ki6syd/minimalist-amateur-xcvr/hw/audio/max-3b_2-2.asc

C1: cap; 100n
C2: cap; 1n
C3: cap; 47n
C4: cap; 1n
C5: cap; 36n
C6: cap; 1n
C7: cap; 39n
C8: cap; 2.2n
C9: cap; 2.2n
C10: cap; 10µ
C11: cap; 10p
C12: cap; 1n
C13: cap; 2n
R1: res; 33k
R2: res; 33k
R3: res; 33k
R4: res; 47k
R5: res; 47k
R6: res; 36k
R7: res; 36k
R8: res; 10k
R9: res; 750k
R10: res; 22k
R11: res; 1k
R12: res; {Rdiv}
R13: res; 49.9k
R14: res; 49.9k
U1: UniversalOpAmp
U2: UniversalOpAmp
U3: UniversalOpAmp
U4: UniversalOpAmp
U5: UniversalOpAmp
V1: voltage; SINE(1.65 10m 700); AC 1
V2: voltage; 3.3
V3: voltage; 1.65
Named nets: 0, VDD, LPF1, LPF2, LPF3, HPF, OUT, IN, VMID, SSB-FILT
*.tran 0 110m 100m
.ac dec 100 100 10k
.step param Rdiv list 100 1Meg
Add 10k to reduce gain
