ki6syd/minimalist-amateur-xcvr/fw/Queue.h

/*
 * Queue.h
 * 
 * By Steven de Salas
 * 
 * Defines a templated (generic) class for a queue of things.
 * Used for Arduino projects, just #include "Queue.h" and add this file via the IDE.
 * 
 * Examples:
 * 
 * Queue<char> queue(10); // Max 10 chars in this queue
 * queue.push('H');
 * queue.push('e');
 * queue.count(); // 2
 * queue.push('l');
 * queue.push('l');
 * queue.count(); // 4
 * Serial.print(queue.pop()); // H
 * Serial.print(queue.pop()); // e
 * queue.count(); // 2
 * queue.push('o');
 * queue.count(); // 3
 * Serial.print(queue.pop()); // l
 * Serial.print(queue.pop()); // l
 * Serial.print(queue.pop()); // o
 * 
 * struct Point { int x; int y; }
 * Queue<Point> points(5);
 * points.push(Point{2,4});
 * points.push(Point{5,0});
 * points.count(); // 2
 * 
 */

#ifndef ARDUINO_QUEUE_H
#define ARDUINO_QUEUE_H

#include <Arduino.h>

template<class T>
class Queue {
  private:
    int _front, _back, _count;
    T *_data;
    int _maxitems;
  public:
    Queue(int maxitems = 256) { 
      _front = 0;
      _back = 0;
      _count = 0;
      _maxitems = maxitems;
      _data = new T[maxitems + 1];   
    }
    ~Queue() {
      delete[] _data;  
    }
    inline int count();
    inline int front();
    inline int back();
    void push(const T &item);
    T peek();
    T pop();
    T cycle();
    void clear();
};

template<class T>
inline int Queue<T>::count() 
{
  return _count;
}

template<class T>
inline int Queue<T>::front() 
{
  return _front;
}

template<class T>
inline int Queue<T>::back() 
{
  return _back;
}

template<class T>
void Queue<T>::push(const T &item)
{
  if(_count < _maxitems) { // Drops out when full
    _data[_back++]=item;
    ++_count;
    // Check wrap around
    if (_back > _maxitems)
      _back -= (_maxitems + 1);
  }
}

template<class T>
T Queue<T>::pop() {
  if(_count <= 0) return T(); // Returns empty
  else {
    T result = _data[_front];
    _front++;
    --_count;
    // Check wrap around
    if (_front > _maxitems) 
      _front -= (_maxitems + 1);
    return result; 
  }
}

template<class T>
T Queue<T>::peek() {
  if(_count <= 0) return T(); // Returns empty
  else return _data[_front];
}

// cycles front element to back, returns the element formerly at the front
// hacky function to give list-like behavior
// not in original library - Max added this
template<class T>
T Queue<T>::cycle() {
  if(_count <= 0) return T(); // Returns empty

  T result = _data[_front];

  // copy front data into back, and increment
  _data[_back++] = result;
  // move front marker up
  _front++;

  // Check wrap around
  if (_back > _maxitems)
    _back -= (_maxitems + 1);
  if (_front > _maxitems) 
      _front -= (_maxitems + 1);
  
  return result;
}

template<class T>
void Queue<T>::clear() 
{
  _front = _back;
  _count = 0;
}

#endif
